GlobalSequence/bing-bong/software/bing_bong_drum_module/bing_bong_math.c

#include "bing_bong_math.h"

#include <Arduino.h>
#include <stdio.h>
#include <math.h>

// int32_t sine2t[SINE2TSIZE + 1];
uint32_t pitcht[PITCHTSIZE];

void bingBongMathInit() {
    // // Sine wave too big to fit in RAM, pre-calculated array below
    // int32_t *p32 = (int32_t *)sine2t;
    // for (int i = 0; i < SINE2TSIZE + 1; i++) {
    //     float f = i * 2 * PI_F / (float)SINE2TSIZE;
    //     *p32++ = (int32_t)(INT32_MAX * sinf(f));
    // }

    uint32_t *q;
    q = (uint32_t *)pitcht;
    for (int i = 0; i < PITCHTSIZE; i++) {
        double f = 440.0 * powf(2.0, (i - 69.0 - 64.0) / 12.0);
        double phi = 4.0 * (double)(1 << 30) * f / (SAMPLE_RATE * 1.0);
        if (phi > ((unsigned int)1 << 31))
            phi = 0x7FFFFFFF;
        *q++ = (uint32_t)phi;
    }
}

const int32_t sine2t[SINE2TSIZE + 1] = { 

0, 3294197, 6588387, 9882561, 13176712, 16470833, 19764912, 23058948, 26352928, 29646846, 32940696, 36234468, 39528152, 42821744, 46115240, 49408620, 
52701888, 55995032, 59288040, 62580916, 65873640, 69166216, 72458624, 75750848, 79042912, 82334784, 85626464, 88917944, 92209208, 95500256, 98791080, 102081680, 
105372032, 108662136, 111951992, 115241576, 118530888, 121819920, 125108672, 128397128, 131685288, 134973120, 138260656, 141547856, 144834720, 148121248, 151407424, 154693248, 
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
1755750016, 1757644800, 1759535488, 1761421952, 1763304320, 1765182464, 1767056512, 1768926336, 1770792064, 1772653568, 1774510976, 1776364160, 1778213248, 1780058112, 1781898752, 1783735168, 
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

 };
